LaskaKit/ESPlan/img/ESPlan (1).jpg

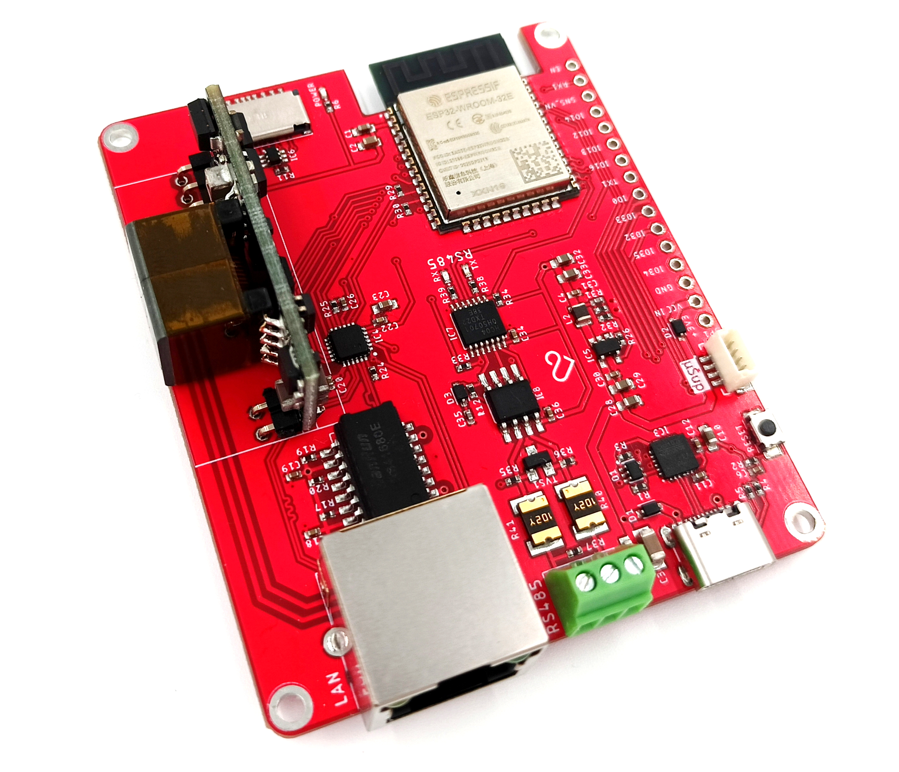
img/ESPlan (1).jpg
