LaskaKit/ESPlan/img/ESPlan (4).jpg

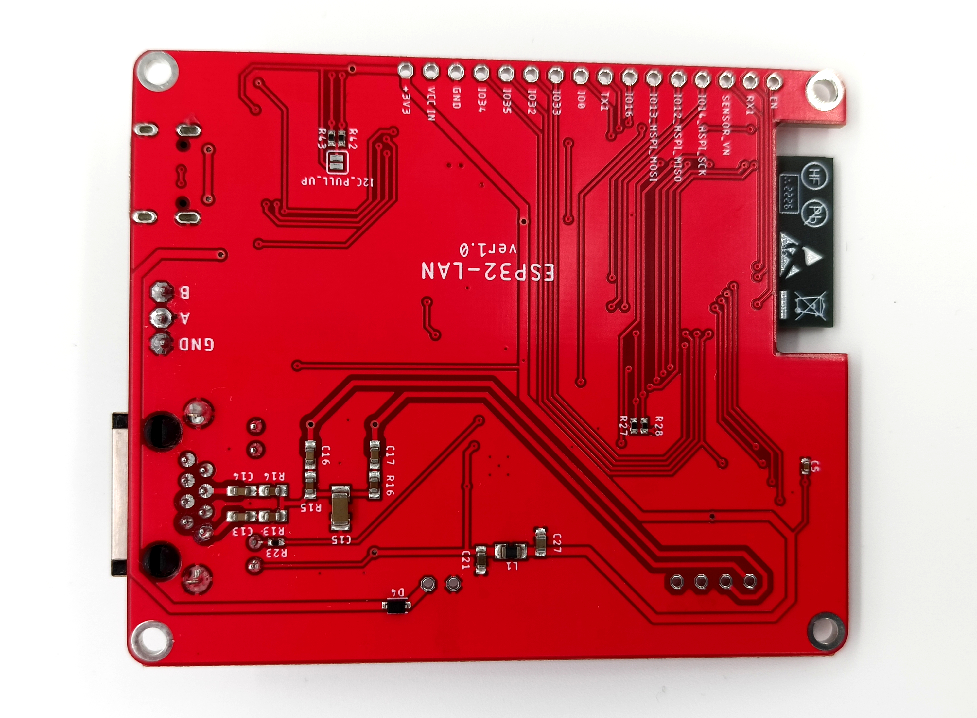
img/ESPlan (4).jpg
