LaskaKit/ESPlan/img/ESPlan (5).jpg

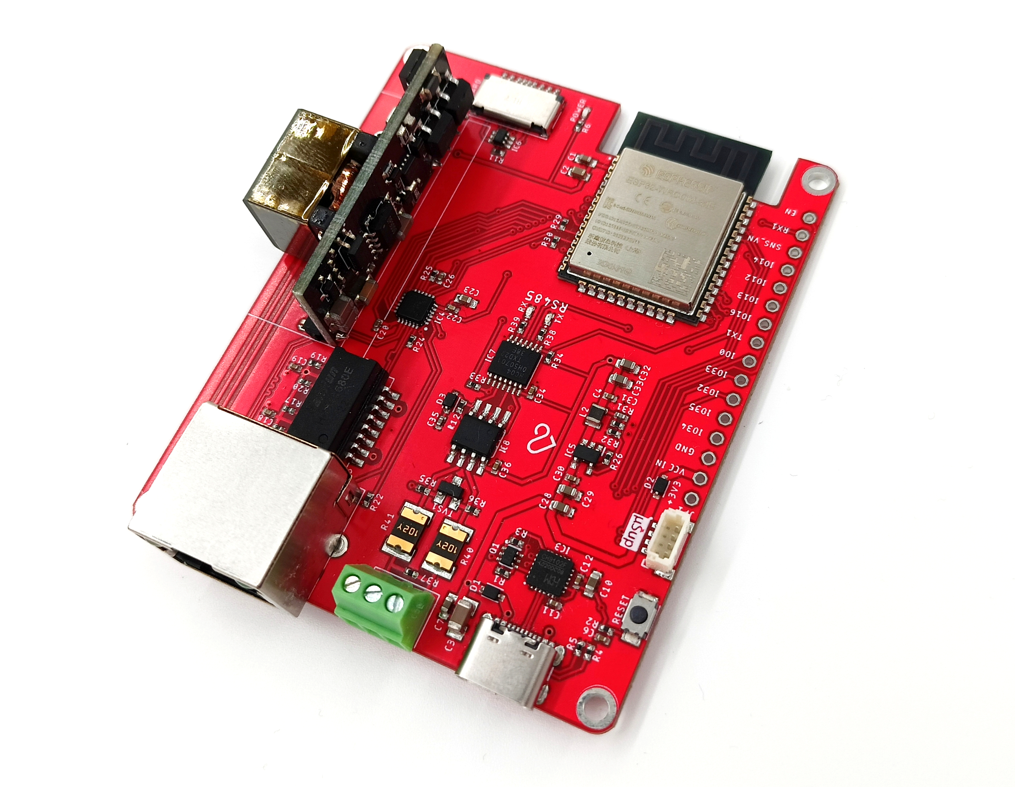
img/ESPlan (5).jpg
