LaskaKit/ESPlan/img/laskakit-esplan-esp32-lan8720a-max485-poe-3.jpg

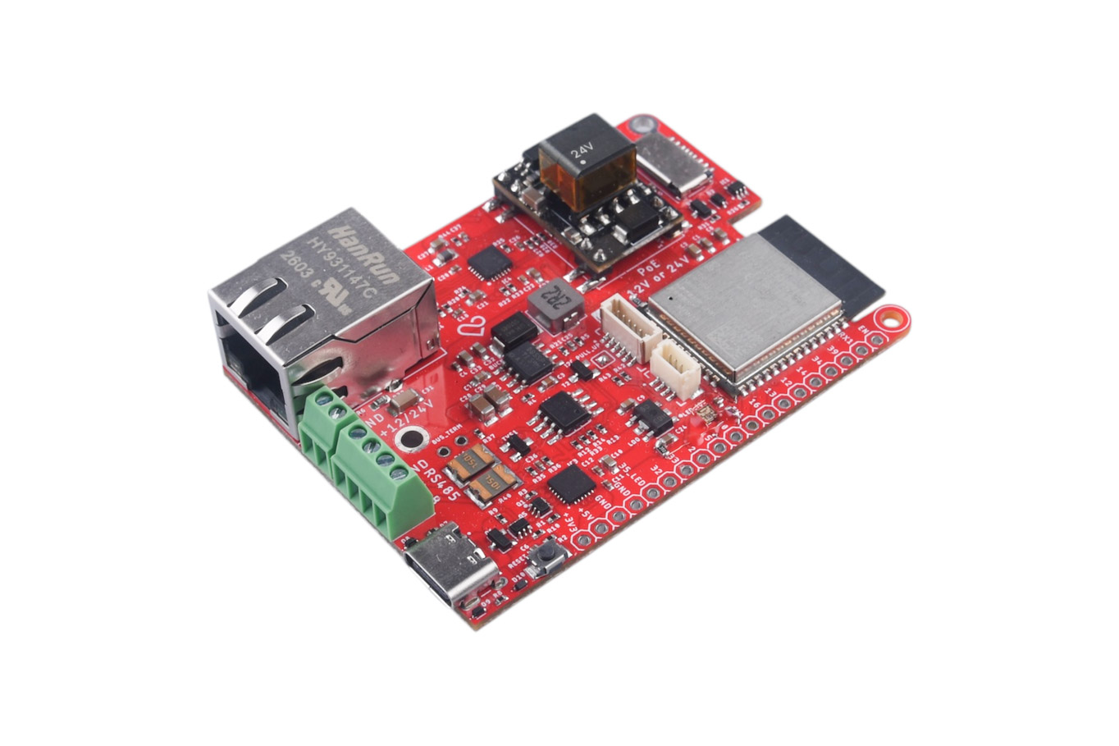
img/laskakit-esplan-esp32-lan8720a-max485-poe-3.jpg
