LaskaKit/ESPlan/img/laskakit-krabicka-pro-laskakit-esplan-v2-3.jpg

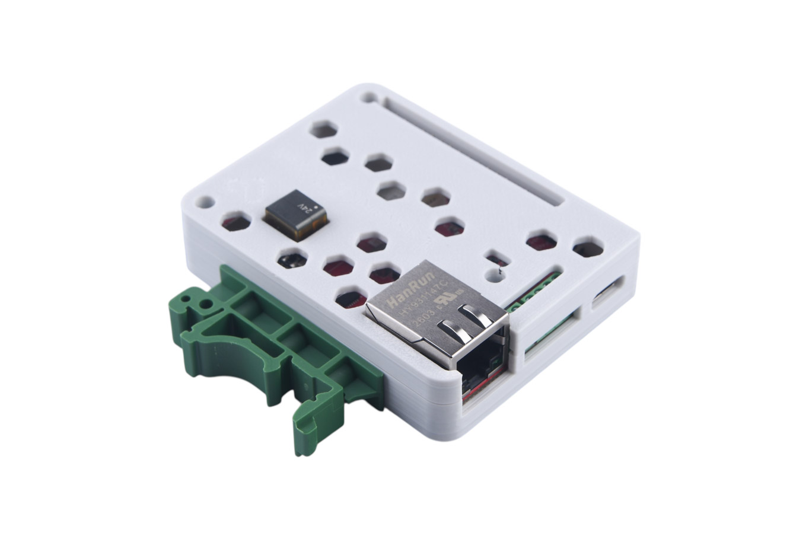
img/laskakit-krabicka-pro-laskakit-esplan-v2-3.jpg
