LaskaKit/ESPlan/img/laskakit-krabicka-pro-laskakit-esplan-v2-4.jpg

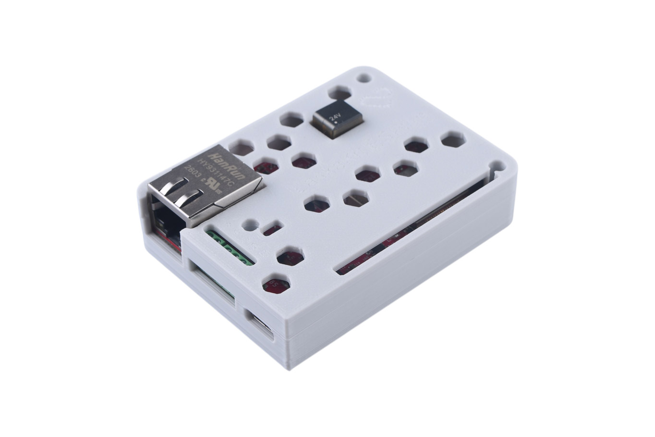
img/laskakit-krabicka-pro-laskakit-esplan-v2-4.jpg
